gtjennings1/UPDuino-LH154Q01-Display/FPGA/source/GPU/drawcircle.v

/******************************************************************************
Copyright 2017 Gnarly Grey LLC

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
THE SOFTWARE IS PROVIDED "AS IS", WITHOUT WARRANTY OF ANY KIND, EXPRESS OR
IMPLIED, INCLUDING BUT NOT LIMITED TO THE WARRANTIES OF MERCHANTABILITY,
FITNESS FOR A PARTICULAR PURPOSE AND NONINFRINGEMENT. IN NO EVENT SHALL THE
AUTHORS OR COPYRIGHT HOLDERS BE LIABLE FOR ANY CLAIM, DAMAGES OR OTHER
LIABILITY, WHETHER IN AN ACTION OF CONTRACT, TORT OR OTHERWISE, ARISING FROM,
OUT OF OR IN CONNECTION WITH THE SOFTWARE OR THE USE OR OTHER DEALINGS IN THE
SOFTWARE.
******************************************************************************/

module drawcircle #(
  
  parameter DATA_WIDTH  = 8           //Parameter for datawidth includes co-ordinates
  
  ) (
  
  input                   clk       , //Clock input
  input                   reset_n   , //Active low reset input
  input                   clk_en    , //Clock enable to slow down output data
  
  input                   enable    , //Trigger to start the function
  
  input  [DATA_WIDTH-1:0] x0        , //Co-ordinate x0
  input  [DATA_WIDTH-1:0] y0        , //Co-ordinate y0
  input  [DATA_WIDTH-1:0] rad       , //Circle radius
  
  output                  valid     , //Output data valid
  output                  done      , //Feedback of task completion
  
  output [DATA_WIDTH-1:0] x_o       , //X co-ordinate output
  output [DATA_WIDTH-1:0] y_o         //Y co-ordinate output
  
  );
  
  parameter UD = 1;  
  parameter FSM_WIDTH = 4;
  parameter IDLE = 4'b0001;
  parameter PREP = 4'b0010;
  parameter DRAW = 4'b0100;
  parameter DONE = 4'b1000;

  reg    [FSM_WIDTH-1:0]  current_state, next_state;
  reg    [DATA_WIDTH-1:0] x0r, y0r, radr;
  reg    [DATA_WIDTH-1:0] xk, yk, x_o_reg, y_o_reg;
  reg    [DATA_WIDTH:0]   delta_x, delta_y, error;

  reg    [2:0]            data_out_seq_cnt;
  reg                     clk_en_fl, valid_reg, done_reg;  
  
  wire                    completed = !( xk < yk); 

  wire                    err_gt_eq_0 = ~error[DATA_WIDTH]; 
  
  wire   [DATA_WIDTH:0]   delta_x_p_2 = delta_x + {{(DATA_WIDTH-1){1'b0}}, 2'b10};
  wire   [DATA_WIDTH:0]   delta_x_p_3 = delta_x + {{(DATA_WIDTH-1){1'b0}}, 2'b11};
  wire   [DATA_WIDTH:0]   delta_y_p_2 = delta_y + {{(DATA_WIDTH-1){1'b0}}, 2'b10};
  wire                    next_iteration = (data_out_seq_cnt == 3'h4);
  
  assign                  x_o   = x_o_reg;
  assign                  y_o   = y_o_reg;
  assign                  valid = valid_reg;
  assign                  done  = done_reg;

  //FSM to keep track of function activity
  always @ (posedge clk or negedge reset_n)
    begin
      if (!reset_n)
        current_state <= #UD IDLE;
      else
        current_state <= #UD next_state;  
    end
  
  always @ (current_state or enable or completed or valid_reg or next_iteration)
    begin
      case(current_state)
        IDLE    : begin
                    if (enable)
                      next_state <= #UD PREP;
                    else
                      next_state <= #UD IDLE;                    
                  end
        PREP    : begin
			              if (valid_reg && next_iteration)
					            next_state <= #UD DRAW;
					          else  
                      next_state <= #UD PREP;
                  end        
        DRAW    : begin
                    if (completed && next_iteration)
                      next_state <= #UD DONE;
                    else
                      next_state <= #UD DRAW;                    
                  end
        DONE    : begin
                    next_state <= #UD IDLE;
                  end
        default : begin
                    next_state <= #UD IDLE;
                  end        
      endcase
    end  
    
  //Store necessary parameters for function in internal registers
  always @ (posedge clk or negedge reset_n)
    begin
      if (!reset_n)
        begin
          x0r  <= #UD {DATA_WIDTH{1'b0}};
          y0r  <= #UD {DATA_WIDTH{1'b0}};
          radr <= #UD {DATA_WIDTH{1'b0}};
        end
      else
      if (enable)
        begin
          x0r  <= #UD x0;
          y0r  <= #UD y0;
          radr <= #UD rad;        
        end
      else
        begin
          x0r  <= #UD x0r;
          y0r  <= #UD y0r;
          radr <= #UD radr;
        end        
    end

  //Process variables
  always @ (posedge clk or negedge reset_n)
    begin
      if (!reset_n)
        begin
          error   <= #UD {(DATA_WIDTH+1){1'b0}};
          delta_x <= #UD {(DATA_WIDTH+1){1'b0}};
          delta_y <= #UD {(DATA_WIDTH+1){1'b0}};          
          xk      <= #UD {DATA_WIDTH{1'b0}};
          yk      <= #UD {DATA_WIDTH{1'b0}};         
        end
      else
        begin
          case (current_state)
            IDLE    : begin
                        error   <= #UD {(DATA_WIDTH+1){1'b0}};
                        delta_x <= #UD {(DATA_WIDTH+1){1'b0}};
                        delta_y <= #UD {(DATA_WIDTH+1){1'b0}};          
                        xk      <= #UD {DATA_WIDTH{1'b0}};
                        yk      <= #UD {DATA_WIDTH{1'b0}};            
                      end
            PREP    : begin
                        error   <= #UD {{(DATA_WIDTH){1'b0}}, 1'b1} - {1'b0, radr};
                        delta_x <= #UD {(DATA_WIDTH+1){1'b0}};
                        delta_y <= #UD {(DATA_WIDTH+1){1'b0}} - {radr, 1'b0};          
                        xk      <= #UD {DATA_WIDTH{1'b0}};
                        yk      <= #UD radr;             
                      end
            DRAW    : begin
                        if (next_iteration && clk_en)
                          begin
                            if (err_gt_eq_0)
                              begin
                                error   <= #UD error + delta_y_p_2 + delta_x_p_3;
                                delta_x <= #UD delta_x_p_2;
                                delta_y <= #UD delta_y_p_2;
                                xk      <= #UD xk + {{(DATA_WIDTH-1){1'b0}}, 1'b1};
                                yk      <= #UD yk - {{(DATA_WIDTH-1){1'b0}}, 1'b1};                            
                              end
                            else
                              begin
                                error   <= #UD error + delta_x_p_3;
                                delta_x <= #UD delta_x_p_2;
                                delta_y <= #UD delta_y;
                                xk      <= #UD xk + {{(DATA_WIDTH-1){1'b0}}, 1'b1};
                                yk      <= #UD yk;                          
                              end
                          end
                        else
                          begin
                              error   <= #UD error;
                              delta_x <= #UD delta_x;
                              delta_y <= #UD delta_y;
                              xk      <= #UD xk;
                              yk      <= #UD yk;                          
                          end                          
                      end
            DONE    : begin
                        error   <= #UD {(DATA_WIDTH+1){1'b0}};
                        delta_x <= #UD {(DATA_WIDTH+1){1'b0}};
                        delta_y <= #UD {(DATA_WIDTH+1){1'b0}};          
                        xk      <= #UD {DATA_WIDTH{1'b0}};
                        yk      <= #UD {DATA_WIDTH{1'b0}};            
                      end
            default : begin
                        error   <= #UD {(DATA_WIDTH+1){1'b0}};
                        delta_x <= #UD {(DATA_WIDTH+1){1'b0}};
                        delta_y <= #UD {(DATA_WIDTH+1){1'b0}};          
                        xk      <= #UD {DATA_WIDTH{1'b0}};
                        yk      <= #UD {DATA_WIDTH{1'b0}};            
                      end
          endcase
        end        
    end
  
  //Data output sequence counter as at a time as many as eight co-ordinates available
  always @ (posedge clk or negedge reset_n)
    begin
      if (!reset_n)
        data_out_seq_cnt <= #UD 3'h0;
      else
      if (current_state == IDLE)
        data_out_seq_cnt <= #UD 3'h0;
      else
      if (clk_en)
        data_out_seq_cnt <= #UD data_out_seq_cnt + 3'h1;
      else
        data_out_seq_cnt <= #UD data_out_seq_cnt;      
    end
  
  //Flop clk_en to synchronize output  
  always @ (posedge clk or negedge reset_n)
    begin
      if (!reset_n)
        clk_en_fl <= #UD 1'b0;
      else
        clk_en_fl <= #UD clk_en;      
    end  
  
  //Generate output co-ordinates
  always @ (posedge clk or negedge reset_n)
    begin
      if (!reset_n)
        begin
          x_o_reg <= #UD {DATA_WIDTH{1'b0}};
          y_o_reg <= #UD {DATA_WIDTH{1'b0}};
        end
      else
        begin
          case (data_out_seq_cnt)
            3'h0    : begin
                        x_o_reg <= #UD x0r - yk;
                        y_o_reg <= #UD y0r - xk;
                      end
            3'h1    : begin
                        x_o_reg <= #UD x0r + xk;
                        y_o_reg <= #UD y0r + yk;            
                      end
            3'h2    : begin
                        x_o_reg <= #UD x0r + xk;
                        y_o_reg <= #UD y0r - yk;            
                      end
            3'h3    : begin
                        x_o_reg <= #UD x0r + yk;
                        y_o_reg <= #UD y0r + xk;            
                      end
            3'h4    : begin
                        x_o_reg <= #UD x0r - yk;
                        y_o_reg <= #UD y0r + xk;            
                      end
            3'h5    : begin
                        x_o_reg <= #UD x0r - xk;
                        y_o_reg <= #UD y0r + yk;            
                      end
            3'h6    : begin
                        x_o_reg <= #UD x0r - xk;
                        y_o_reg <= #UD y0r - yk;            
                      end
            3'h7    : begin
                        x_o_reg <= #UD x0r + yk;
                        y_o_reg <= #UD y0r - xk;            
                      end
            default : begin
                        x_o_reg <= #UD x_o_reg;
                        y_o_reg <= #UD y_o_reg;            
                      end
          endcase
        end        
    end    
    
  //Generate valid signal
  always @ (posedge clk or negedge reset_n)
    begin
      if (!reset_n)
        valid_reg <= #UD 1'b0;
      else
      if (clk_en_fl)
        case(current_state)
          IDLE    : valid_reg <= #UD 1'b0;
          PREP    : valid_reg <= #UD 1'b1;
          DRAW    : valid_reg <= #UD 1'b1;
          DONE    : valid_reg <= #UD 1'b0;
          default : valid_reg <= #UD 1'b0;
        endcase
      else
        valid_reg <= #UD 1'b0;      
    end
  
  //Generate done signal
  always @ (posedge clk or negedge reset_n)
    begin
      if (!reset_n)
        done_reg <= #UD 1'b0;
      else
      if (current_state == DONE)
        done_reg <= #UD 1'b1;
      else
        done_reg <= #UD 1'b0;      
    end    
  
endmodule  
