gtjennings1/UPDuino-LH154Q01-Display/FPGA/source/GPU/generic_fifo_lfsr.v

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
//
//  CVS Log
//
//  $Id: generic_fifo_lfsr.v,v 1.1 2002-10-29 19:45:07 rherveille Exp $
//
//  $Date: 2002-10-29 19:45:07 $
//  $Revision: 1.1 $
//  $Author: rherveille $
//  $Locker:  $
//  $State: Exp $
//
// Change History:
//               $Log: not supported by cvs2svn $

//`include "timescale.v"
`timescale 1ns/100ps

// set FIFO_RW_CHECK to prevent writing to a full and reading from an empty FIFO
//`define FIFO_RW_CHECK

// Long Pseudo Random Generators can generate (N^2 -1) combinations. This means
// 1 FIFO entry is unavailable. This might be a problem, especially for small
// FIFOs. Setting FIFO_ALL_ENTRIES creates additional logic that ensures that
// all FIFO entries are used at the expense of some additional logic.
`define FIFO_ALL_ENTRIES
`define RW_CHECK

module generic_fifo_lfsr (
	clk,
	nReset,
	rst,
	wreq,
	rreq,
	d,
	q,
	empty,
	full,
	aempty,
	afull
	);

	//
	// parameters
	//
	parameter aw =  8;                         // no.of entries (in bits; 2^7=128 entries)
	parameter dw =  32;                         // datawidth (in bits)

	//
	// inputs & outputs
	//
	input             clk;                     // master clock
	input nReset;                              // asynchronous active low reset
	input rst;                                 // synchronous active high reset

	input             wreq;                    // write request
	input             rreq;                    // read request
	input  [dw:1] d;                           // data-input
	output [dw:1] q;                           // data-output

	output            empty;                   // fifo empty
	output            full;                    // fifo full

	output            aempty;                  // fifo asynchronous/almost empty (1 entry left)
	output            afull;                   // fifo asynchronous/almost full (1 entry left)

	reg empty, full;

	//
	// Module body
	//
	reg  [aw:1] rp, wp;
	wire [dw:1] ramq;
	wire fwreq, frreq;

`ifdef FIFO_ALL_ENTRIES
	function lsb;
	   input [aw:1] q;
	   case (aw)
	       2: lsb = ~q[2];
	       3: lsb = &q[aw-1:1] ^ ~(q[3] ^ q[2]);
	       4: lsb = &q[aw-1:1] ^ ~(q[4] ^ q[3]);
	       5: lsb = &q[aw-1:1] ^ ~(q[5] ^ q[3]);
	       6: lsb = &q[aw-1:1] ^ ~(q[6] ^ q[5]);
	       7: lsb = &q[aw-1:1] ^ ~(q[7] ^ q[6]);
	       8: lsb = &q[aw-1:1] ^ ~(q[8] ^ q[6] ^ q[5] ^ q[4]);
	       9: lsb = &q[aw-1:1] ^ ~(q[9] ^ q[5]);
	      10: lsb = &q[aw-1:1] ^ ~(q[10] ^ q[7]);
	      11: lsb = &q[aw-1:1] ^ ~(q[11] ^ q[9]);
	      12: lsb = &q[aw-1:1] ^ ~(q[12] ^ q[6] ^ q[4] ^ q[1]);
	      13: lsb = &q[aw-1:1] ^ ~(q[13] ^ q[4] ^ q[3] ^ q[1]);
	      14: lsb = &q[aw-1:1] ^ ~(q[14] ^ q[5] ^ q[3] ^ q[1]);
	      15: lsb = &q[aw-1:1] ^ ~(q[15] ^ q[14]);
	      16: lsb = &q[aw-1:1] ^ ~(q[16] ^ q[15] ^ q[13] ^ q[4]);
	   endcase
	endfunction
`else
	function lsb;
	   input [aw:1] q;
	   case (aw)
	       2: lsb = ~q[2];
	       3: lsb = ~(q[3] ^ q[2]);
	       4: lsb = ~(q[4] ^ q[3]);
	       5: lsb = ~(q[5] ^ q[3]);
	       6: lsb = ~(q[6] ^ q[5]);
	       7: lsb = ~(q[7] ^ q[6]);
	       8: lsb = ~(q[8] ^ q[6] ^ q[5] ^ q[4]);
	       9: lsb = ~(q[9] ^ q[5]);
	      10: lsb = ~(q[10] ^ q[7]);
	      11: lsb = ~(q[11] ^ q[9]);
	      12: lsb = ~(q[12] ^ q[6] ^ q[4] ^ q[1]);
	      13: lsb = ~(q[13] ^ q[4] ^ q[3] ^ q[1]);
	      14: lsb = ~(q[14] ^ q[5] ^ q[3] ^ q[1]);
	      15: lsb = ~(q[15] ^ q[14]);
	      16: lsb = ~(q[16] ^ q[15] ^ q[13] ^ q[4]);
	   endcase
	endfunction
`endif

`ifdef RW_CHECK
  assign fwreq = wreq & ~full;
  assign frreq = rreq & ~empty;
`else
  assign fwreq = wreq;
  assign frreq = rreq;
`endif

	// hookup read-pointer
	always @(posedge clk or negedge nReset)
	  if (~nReset)    rp <= #1 0;
	  else if (rst)   rp <= #1 0;
	  else if (frreq) rp <= #1 {rp[aw-1:1], lsb(rp)};

	// hookup write-pointer
	always @(posedge clk or negedge nReset)
	  if (~nReset)    wp <= #1 0;
	  else if (rst)   wp <= #1 0;
	  else if (fwreq) wp <= #1 {wp[aw-1:1], lsb(wp)};

	// hookup RAM-block
	// generic_dpram #(aw, dw)
	// fiforam (
		// // write section
		// .wclk(clk),
		// .wrst(1'b0),
		// .wce(1'b1),
		// .we(fwreq),
		// .waddr(wp),
		// .di(d),
//
		// // read section
		// .rclk(clk),
		// .rrst(1'b0),
		// .rce(1'b1),
		// .oe(1'b1),
		// .raddr(rp),
		// .do(q)
	// );

  SB_RAM256x16 ram256x16_wrfifo0 (
    .RDATA  (q[dw/2:1]),
    .RADDR  (rp),
    .RCLK   (clk),
    .RCLKE  (1'b1),
    .RE     (frreq),
    .WADDR  (wp),
    .WCLK   (clk),
    .WCLKE  (1'b1),
    .WDATA  (d[dw/2:1]),
    .WE     (fwreq),
    .MASK   (16'h0000)
  );

  SB_RAM256x16 ram256x16_wrfifo1 (
    .RDATA  (q[dw:(dw/2)+1]),
    .RADDR  (rp),
    .RCLK   (clk),
    .RCLKE  (1'b1),
    .RE     (frreq),
    .WADDR  (wp),
    .WCLK   (clk),
    .WCLKE  (1'b1),
    .WDATA  (d[dw:(dw/2)+1]),
    .WE     (fwreq),
    .MASK   (16'h0000)
  );

	// generate full/empty signals
	assign aempty = (rp[aw-1:1] == wp[aw:2]) & (lsb(rp) == wp[1]) & frreq & ~fwreq;
	always @(posedge clk or negedge nReset)
	  if (~nReset)
	    empty <= #1 1'b1;
	  else if (rst)
	    empty <= #1 1'b1;
	  else
	    empty <= #1 aempty | (empty & (~fwreq + frreq));

	assign afull = (wp[aw-1:1] == rp[aw:2]) & (lsb(wp) == rp[1]) & fwreq & ~frreq;
	always @(posedge clk or negedge nReset)
	  if (~nReset)
	    full <= #1 1'b0;
	  else if (rst)
	    full <= #1 1'b0;
	  else
	    full <= #1 afull | ( full & (~frreq + fwreq) );

	//
	// Simulation checks
	//
	// synopsys translate_off
	always @(posedge clk)
	  if (full & fwreq)
	    $display("Writing while FIFO full\n");

	always @(posedge clk)
	  if (empty & frreq)
	    $display("Reading while FIFO empty\n");
	// synopsys translate_on
endmodule
