gtjennings1/UPDuino-LH154Q01-Display/Arduino/upduino_bitmap_demo2/bitmap.h

/******************************************************************************
Copyright 2017 Gnarly Grey LLC

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
THE SOFTWARE IS PROVIDED "AS IS", WITHOUT WARRANTY OF ANY KIND, EXPRESS OR
IMPLIED, INCLUDING BUT NOT LIMITED TO THE WARRANTIES OF MERCHANTABILITY,
FITNESS FOR A PARTICULAR PURPOSE AND NONINFRINGEMENT. IN NO EVENT SHALL THE
AUTHORS OR COPYRIGHT HOLDERS BE LIABLE FOR ANY CLAIM, DAMAGES OR OTHER
LIABILITY, WHETHER IN AN ACTION OF CONTRACT, TORT OR OTHERWISE, ARISING FROM,
OUT OF OR IN CONNECTION WITH THE SOFTWARE OR THE USE OR OTHER DEALINGS IN THE
SOFTWARE.
******************************************************************************/

// Generated by  : ImageConverter 565 v2.2
// Generated from: candy.png
// Time generated: 04-09-2017 12:37:29
// Dimensions    : 64x64 pixels
// Size          : 8,192 Bytes

const uint16_t candyCBM[] PROGMEM ={
0x0000, 0x0000, 0x0000, 0x0000, 0x0000, 0x0000, 0x0000, 0x0000, 0x0000, 0x0000, 0x0000, 0x0000, 0x0000, 0x0000, 0x0000, 0x0000,   // 0x0010 (16)
0x0000, 0x0000, 0x0000, 0x3143, 0x3924, 0x3944, 0x3944, 0x3144, 0x3123, 0x3964, 0x39A4, 0x39A3, 0x39C2, 0x39E0, 0x0000, 0x0000,   // 0x0020 (32)
0x0000, 0x0000, 0x0000, 0x0000, 0x0000, 0x0000, 0x0000, 0x0000, 0x0000, 0x0000, 0x0000, 0x0000, 0x0000, 0x0000, 0x0000, 0x0000,   // 0x0030 (48)
0x0000, 0x0000, 0x0000, 0x0000, 0x0000, 0x0000, 0x0000, 0x0000, 0x0000, 0x0000, 0x0000, 0x0000, 0x0000, 0x0000, 0x0000, 0x0000,   // 0x0040 (64)
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
0xF579, 0xF579, 0xF579, 0xED59, 0xED58, 0xED38, 0xE518, 0xE4F7, 0xDCD6, 0xD496, 0xD455, 0xD455, 0xA310, 0x0000, 0x0000, 0x0000,   // 0x0270 (624)
0x0000, 0x0000, 0x0000, 0x0000, 0x0000, 0x0000, 0x0000, 0x0000, 0x0000, 0x0000, 0x0000, 0x0000, 0x0000, 0x0000, 0x0000, 0x0000,   // 0x0280 (640)
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
};
