gtjennings1/UPDuino-LH154Q01-Display/Arduino/upduino_bm_font_demo1/FreeSans9pt7b.h

const uint8_t FreeSans9pt7bBitmaps[] PROGMEM = {
  0xFF, 0xFF, 0xF8, 0xC0, 0xDE, 0xF7, 0x20, 0x09, 0x86, 0x41, 0x91, 0xFF,
  0x13, 0x04, 0xC3, 0x20, 0xC8, 0xFF, 0x89, 0x82, 0x61, 0x90, 0x10, 0x1F,
  0x14, 0xDA, 0x3D, 0x1E, 0x83, 0x40, 0x78, 0x17, 0x08, 0xF4, 0x7A, 0x35,
  0x33, 0xF0, 0x40, 0x20, 0x38, 0x10, 0xEC, 0x20, 0xC6, 0x20, 0xC6, 0x40,
  0xC6, 0x40, 0x6C, 0x80, 0x39, 0x00, 0x01, 0x3C, 0x02, 0x77, 0x02, 0x63,
  0x04, 0x63, 0x04, 0x77, 0x08, 0x3C, 0x0E, 0x06, 0x60, 0xCC, 0x19, 0x81,
  0xE0, 0x18, 0x0F, 0x03, 0x36, 0xC2, 0xD8, 0x73, 0x06, 0x31, 0xE3, 0xC4,
  0xFE, 0x13, 0x26, 0x6C, 0xCC, 0xCC, 0xC4, 0x66, 0x23, 0x10, 0x8C, 0x46,
  0x63, 0x33, 0x33, 0x32, 0x66, 0x4C, 0x80, 0x25, 0x7E, 0xA5, 0x00, 0x30,
  0xC3, 0x3F, 0x30, 0xC3, 0x0C, 0xD6, 0xF0, 0xC0, 0x08, 0x44, 0x21, 0x10,
  0x84, 0x42, 0x11, 0x08, 0x00, 0x3C, 0x66, 0x42, 0xC3, 0xC3, 0xC3, 0xC3,
  0xC3, 0xC3, 0xC3, 0x42, 0x66, 0x3C, 0x11, 0x3F, 0x33, 0x33, 0x33, 0x33,
  0x30, 0x3E, 0x31, 0xB0, 0x78, 0x30, 0x18, 0x1C, 0x1C, 0x1C, 0x18, 0x18,
  0x10, 0x08, 0x07, 0xF8, 0x3C, 0x66, 0xC3, 0xC3, 0x03, 0x06, 0x1C, 0x07,
  0x03, 0xC3, 0xC3, 0x66, 0x3C, 0x0C, 0x18, 0x71, 0x62, 0xC9, 0xA3, 0x46,
  0xFE, 0x18, 0x30, 0x60, 0xC0, 0x7F, 0x20, 0x10, 0x08, 0x08, 0x07, 0xF3,
  0x8C, 0x03, 0x01, 0x80, 0xF0, 0x6C, 0x63, 0xE0, 0x1E, 0x31, 0x98, 0x78,
  0x0C, 0x06, 0xF3, 0x8D, 0x83, 0xC1, 0xE0, 0xD0, 0x6C, 0x63, 0xE0, 0xFF,
  0x03, 0x02, 0x06, 0x04, 0x0C, 0x08, 0x18, 0x18, 0x18, 0x10, 0x30, 0x30,
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
  {   429,   8,  13,  11,    1,  -12 },   // 0x46 'F'
  {   442,  12,  13,  14,    1,  -12 },   // 0x47 'G'
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

const GFXfont FreeSans9pt7b PROGMEM = {
  (uint8_t  *)FreeSans9pt7bBitmaps,
  (GFXglyph *)FreeSans9pt7bGlyphs,
  0x20, 0x7E, 22 };

// Approx. 1822 bytes
