gtjennings1/UPDuino-LH154Q01-Display/Arduino/upduino_bm_font_demo1/chinese_bold12pt7b.h

/******************************************************************************
Copyright 2017 Gnarly Grey LLC

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
THE SOFTWARE IS PROVIDED "AS IS", WITHOUT WARRANTY OF ANY KIND, EXPRESS OR
IMPLIED, INCLUDING BUT NOT LIMITED TO THE WARRANTIES OF MERCHANTABILITY,
FITNESS FOR A PARTICULAR PURPOSE AND NONINFRINGEMENT. IN NO EVENT SHALL THE
AUTHORS OR COPYRIGHT HOLDERS BE LIABLE FOR ANY CLAIM, DAMAGES OR OTHER
LIABILITY, WHETHER IN AN ACTION OF CONTRACT, TORT OR OTHERWISE, ARISING FROM,
OUT OF OR IN CONNECTION WITH THE SOFTWARE OR THE USE OR OTHER DEALINGS IN THE
SOFTWARE.
******************************************************************************/

const uint8_t chinese_bold12pt7bBitmaps[] PROGMEM = {
  0x1F, 0xF2, 0xA0, 0x7A, 0x18, 0x61, 0x85, 0xE0, 0x01, 0xC1, 0x83, 0x04,
  0x00, 0x23, 0x30, 0x82, 0x08, 0x20, 0x82, 0x08, 0x20, 0x82, 0x08, 0x20,
  0x82, 0x08, 0x10, 0x30, 0x30, 0x00, 0x01, 0x03, 0x03, 0x04, 0x10, 0x41,
  0x04, 0x10, 0x41, 0x04, 0x10, 0x41, 0x04, 0x10, 0x42, 0x33, 0x00, 0x00,
  0x00, 0x00, 0x00, 0x01, 0x80, 0x00, 0x01, 0x00, 0x04, 0x04, 0x00, 0x1F,
  0xFF, 0xF8, 0x40, 0x00, 0x43, 0x00, 0x01, 0x08, 0x00, 0x28, 0x07, 0xFF,
  0xC0, 0x00, 0x06, 0x00, 0x00, 0x60, 0x00, 0x06, 0x00, 0x00, 0x10, 0x00,
  0x00, 0x40, 0x67, 0xFF, 0xFF, 0xC0, 0x04, 0x00, 0x00, 0x10, 0x00, 0x00,
  0x40, 0x00, 0x01, 0x00, 0x00, 0x04, 0x00, 0x00, 0xF0, 0x00, 0x00, 0x80,
  0x00, 0x00, 0x00, 0x00, 0x40, 0x01, 0x00, 0xFF, 0xFE, 0x02, 0x08, 0x10,
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
  {  1749,  21,  20,  24,    1,  -18 },   // 0x43 'C'
  {  1802,  19,  22,  24,    2,  -19 },   // 0x44 'D'
  {  1855,  22,  22,  24,    1,  -19 },   // 0x45 'E'
  {  1916,  22,  20,  24,    1,  -17 },   // 0x46 'F'
  {  1971,  22,  22,  24,    1,  -19 },   // 0x47 'G'
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

const GFXfont chinese_bold12pt7b PROGMEM = {
  (uint8_t  *)chinese_bold12pt7bBitmaps,
  (GFXglyph *)chinese_bold12pt7bGlyphs,
  0x20, 0x7E, 27 };

// Approx. 5785 bytes
