gtjennings1/UPDuino-LH154Q01-Display/Arduino/upduino_bm_font_demo1/chinese_norm12pt7b.h

/******************************************************************************
Copyright 2017 Gnarly Grey LLC

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
THE SOFTWARE IS PROVIDED "AS IS", WITHOUT WARRANTY OF ANY KIND, EXPRESS OR
IMPLIED, INCLUDING BUT NOT LIMITED TO THE WARRANTIES OF MERCHANTABILITY,
FITNESS FOR A PARTICULAR PURPOSE AND NONINFRINGEMENT. IN NO EVENT SHALL THE
AUTHORS OR COPYRIGHT HOLDERS BE LIABLE FOR ANY CLAIM, DAMAGES OR OTHER
LIABILITY, WHETHER IN AN ACTION OF CONTRACT, TORT OR OTHERWISE, ARISING FROM,
OUT OF OR IN CONNECTION WITH THE SOFTWARE OR THE USE OR OTHER DEALINGS IN THE
SOFTWARE.
******************************************************************************/

const uint8_t chinese_norm12pt7bBitmaps[] PROGMEM = {
  0x39, 0xF7, 0xCF, 0x18, 0xE7, 0x18, 0x3C, 0x7E, 0xE7, 0xC3, 0xC3, 0xC3,
  0xE7, 0x7E, 0x3C, 0x60, 0xF0, 0xFC, 0x7E, 0x1F, 0x0F, 0x06, 0x0E, 0x7D,
  0xF7, 0x8E, 0x1C, 0x38, 0x70, 0xE1, 0xC3, 0x87, 0x0E, 0x1C, 0x38, 0x70,
  0xE1, 0xC3, 0x87, 0x87, 0xC7, 0xC3, 0x80, 0xE1, 0xF1, 0xF0, 0xF0, 0xE1,
  0xC3, 0x87, 0x0E, 0x1C, 0x38, 0x70, 0xE1, 0xC3, 0x87, 0x0E, 0x1C, 0x38,
  0xF7, 0xDF, 0x38, 0x00, 0x00, 0x38, 0x00, 0x00, 0xE0, 0x00, 0x03, 0x80,
  0x1F, 0xFF, 0xFE, 0x7F, 0xFF, 0xFD, 0x80, 0x00, 0x76, 0x00, 0x01, 0xDF,
  0xFF, 0xFE, 0x7F, 0xFF, 0xF8, 0x00, 0x3F, 0x00, 0x03, 0xF0, 0x00, 0x1F,
  0x80, 0x00, 0x78, 0x00, 0x01, 0xE0, 0x0F, 0xFF, 0xFF, 0xFF, 0xFF, 0xFF,
  0x00, 0x0E, 0x00, 0x00, 0x38, 0x00, 0x00, 0xE0, 0x01, 0x07, 0x80, 0x0F,
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
  {  1892,  23,  21,  24,    0,  -19 },   // 0x43 'C'
  {  1953,  20,  23,  24,    2,  -19 },   // 0x44 'D'
  {  2011,  22,  23,  24,    1,  -19 },   // 0x45 'E'
  {  2075,  22,  21,  24,    1,  -17 },   // 0x46 'F'
  {  2133,  22,  23,  24,    1,  -19 },   // 0x47 'G'
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

const GFXfont chinese_norm12pt7b PROGMEM = {
  (uint8_t  *)chinese_norm12pt7bBitmaps,
  (GFXglyph *)chinese_norm12pt7bGlyphs,
  0x20, 0x7E, 27 };

// Approx. 6211 bytes
